golioth/elixir-hw/input/mech/ControlledImpedanceAludelElixirRevA.png

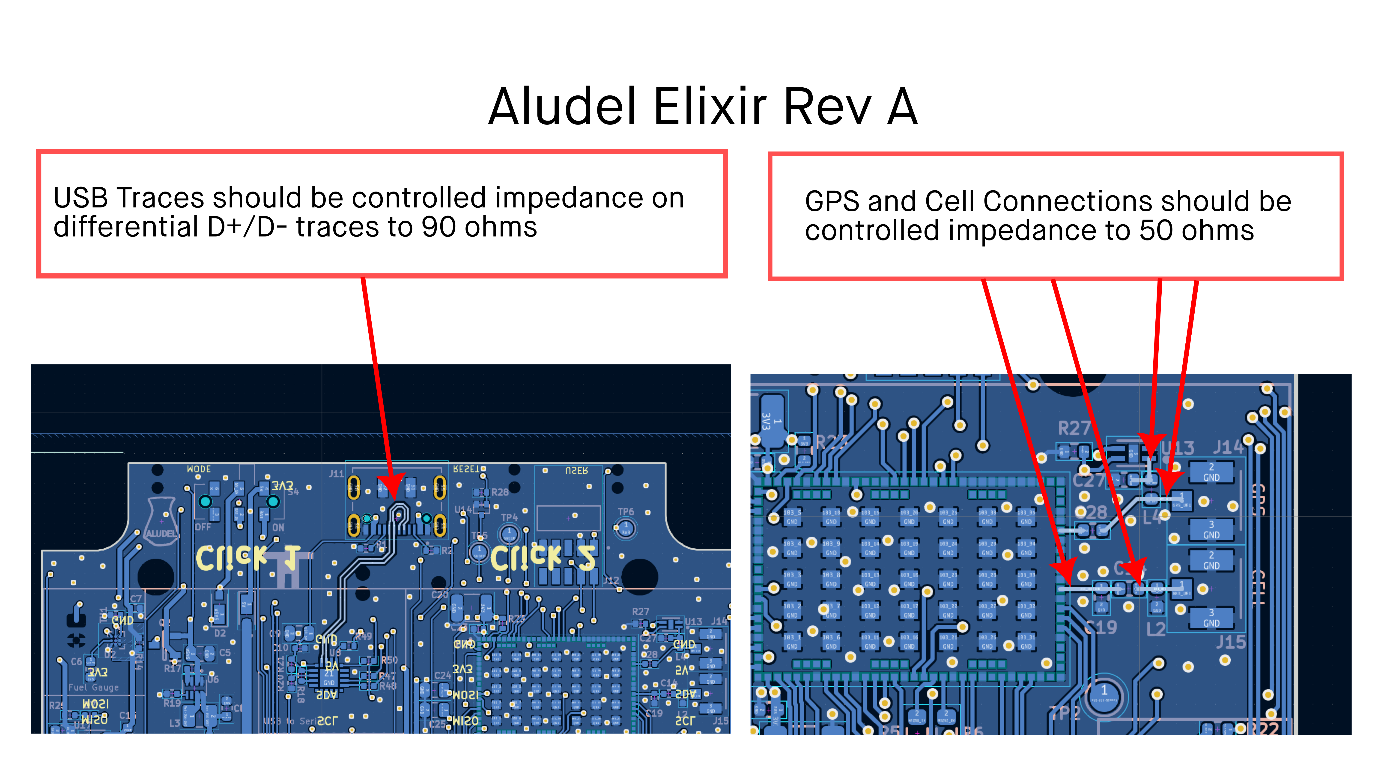
input/mech/ControlledImpedanceAludelElixirRevA.png
