golioth/elixir-hw/input/mech/env_combo_breakout_dimensions.jpg

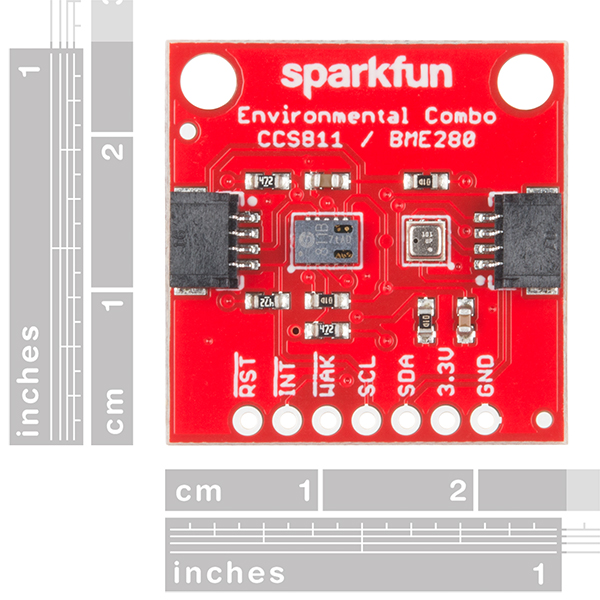
input/mech/env_combo_breakout_dimensions.jpg
