golioth/elixir-hw/input/mech/TOF_board_image.jpg

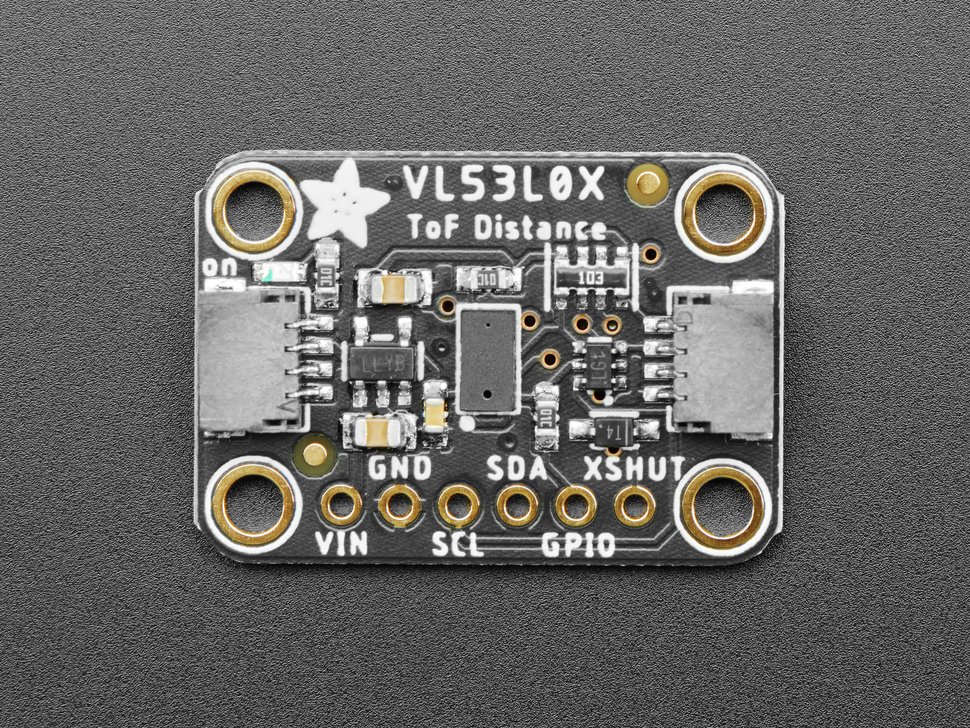
input/mech/TOF_board_image.jpg
