golioth/elixir-hw/input/3d/MIC2288YD5-TR.step

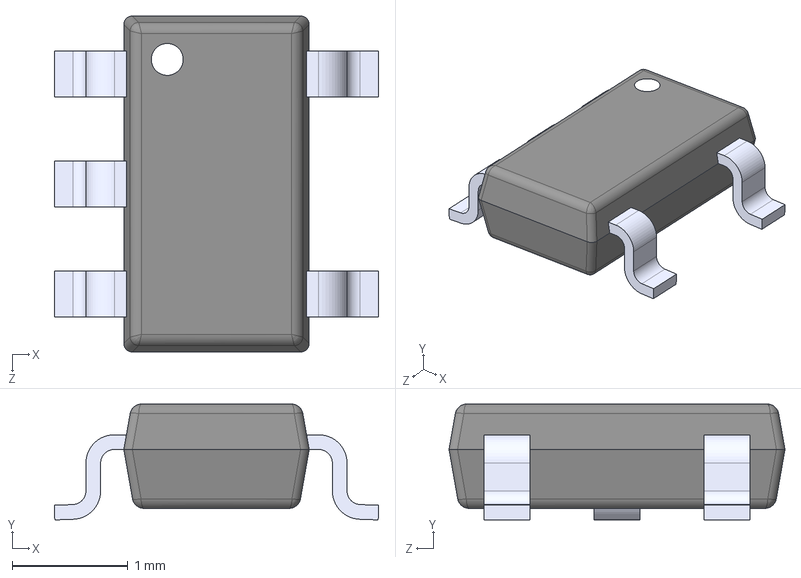
[picture p24: CAD file, 2024-07-08]
input/3d/MIC2288YD5-TR.step
2.80 x 1.00 x 2.90 mm
