golioth/elixir-hw/input/3d/LQH32CN4R7M33L.step

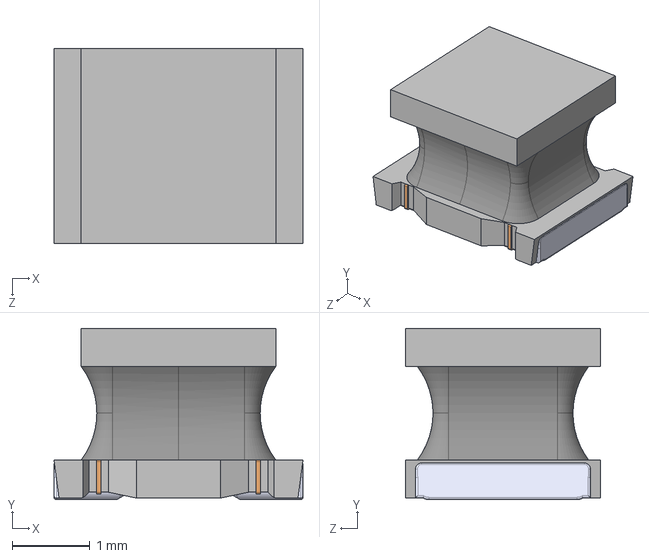
[picture p25: CAD file, 2024-07-08]
input/3d/LQH32CN4R7M33L.step
3.20 x 2.20 x 2.50 mm
