golioth/elixir-hw/input/3d/DX07S016JA1R1500.step

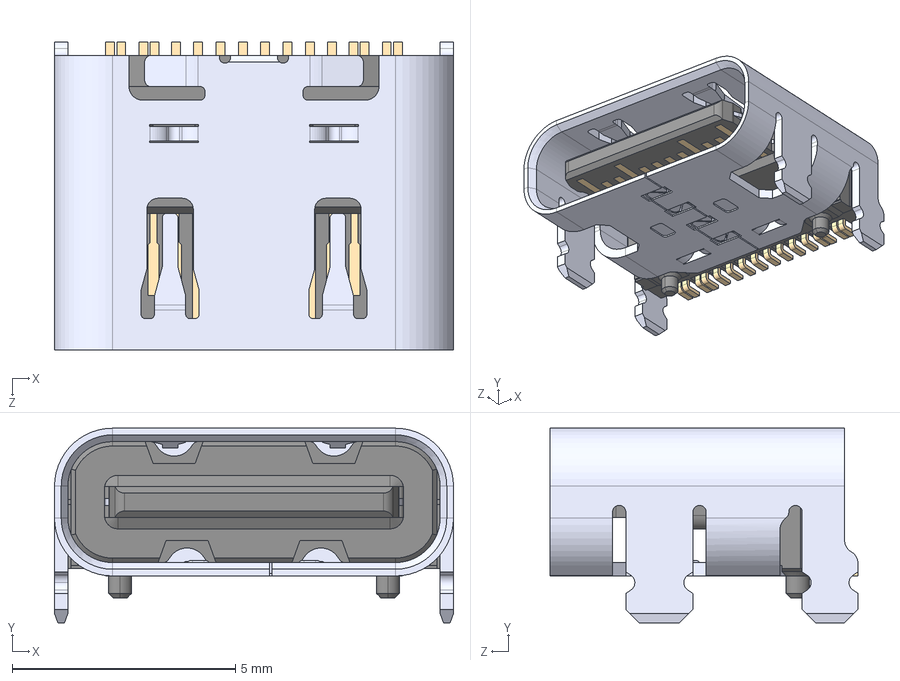
[picture p26: CAD file, 2024-07-08]
input/3d/DX07S016JA1R1500.step
8.94 x 4.36 x 6.90 mm
