golioth/elixir-hw/input/3d/EVQ-P7L01P.step

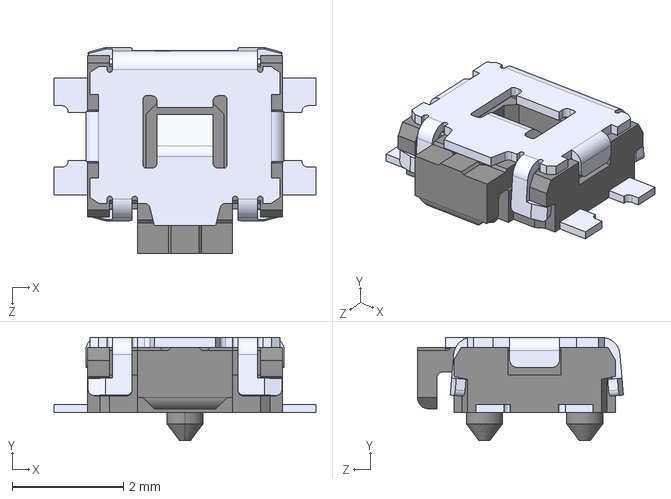
[picture p27: CAD file, 2024-07-08]
input/3d/EVQ-P7L01P.step
4.70 x 1.85 x 3.69 mm
