golioth/elixir-hw/input/3d/NRF9160-SIBA-R.step

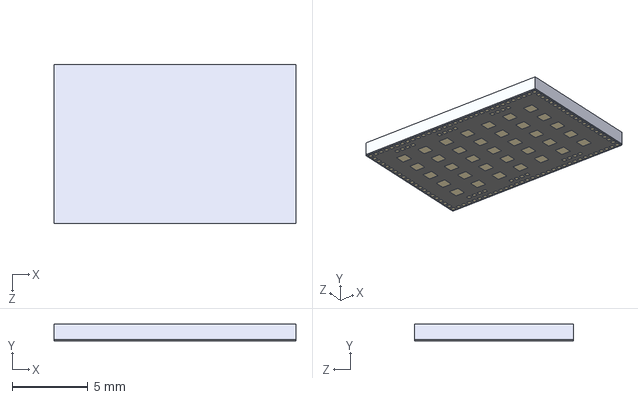
[picture p28: CAD file, 2024-07-08]
input/3d/NRF9160-SIBA-R.step
16.0 x 1.10 x 10.5 mm
